Jose-Amaya/Proyecto-Introduccion/4. Página web/html/img/bk/IMG_20180207_075633.jpg

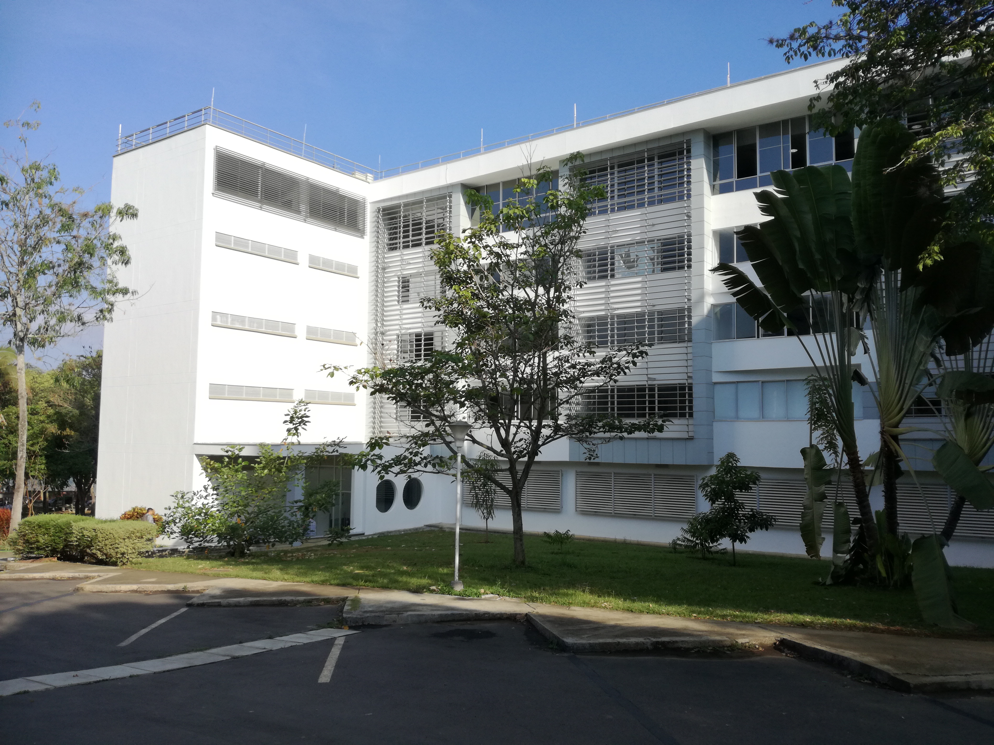
4. Página web/html/img/bk/IMG_20180207_075633.jpg
